koNrand/RIAA_phono_preamp/simulation_LTSpice.asc

C1: cap; 220n
C2: cap; 22n
C3: cap; 10µ
C4: cap; 1µ
R1: res; 150k
R2: res; 150k
R3: res; 72k
R4: res; 47k
R5: res; 100
R6: res; 100k
R7: res; 10k
R8: res; 1k
R9: res; 1k
U1: OP07
U2: OP07
V1: voltage; ""; AC 1
V2: voltage; 5
Named nets: 0, 5V
.ac dec 20 2 20k
